MZandtheRaspberryPi/holiday_project_2022/hardware/minibat bot.png

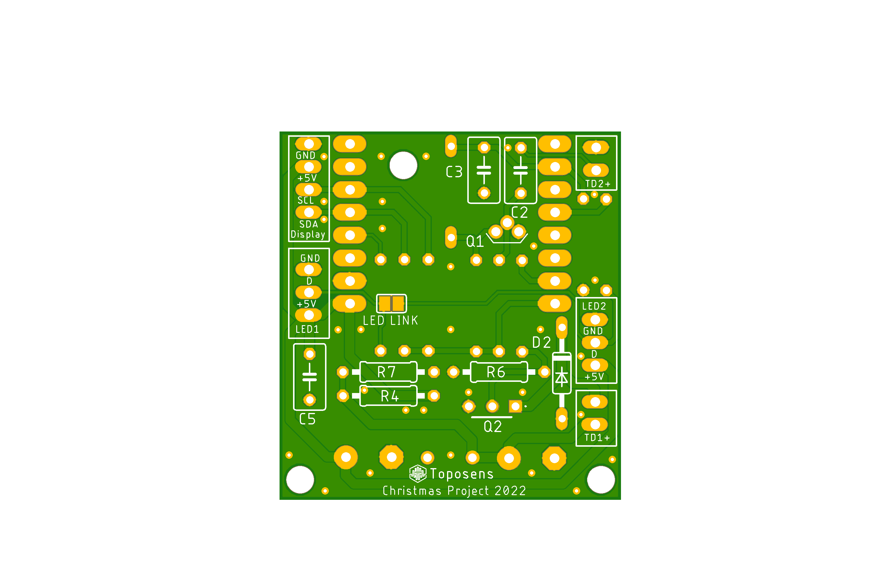
hardware/minibat bot.png
