MZandtheRaspberryPi/holiday_project_2022/firmware/src/oled.cpp

#include "oled.h"

#include <Arduino.h>
#include <Wire.h>
#include <Adafruit_GFX.h>
#include <Adafruit_SSD1306.h>

#include "pins.h"
#include "animate_face.h"

#define SCREEN_BUFFER_HEIGHT    (SCREEN_HEIGHT / 8) // 8 Pixel in a column are packed into one byte

Adafruit_SSD1306 display(SCREEN_WIDTH, SCREEN_HEIGHT, &Wire, -1, 400000, 400000);
static bool showAdcData = false;

void Show_ADC_Data(bool show)
{
    showAdcData = show;
}

void Frame_Shift(FRAME_ShiftDirection_e direction, FRAME_Part_e framePart = FRAME_PART_FULL)
{
    uint8_t height = framePart == FRAME_PART_FULL ? SCREEN_BUFFER_HEIGHT : SCREEN_BUFFER_HEIGHT / 2;
    uint16_t offset = framePart == FRAME_PART_BOT ? (SCREEN_WIDTH * SCREEN_BUFFER_HEIGHT / 2) : 0;
    uint8_t* displayBuffer = display.getBuffer();

    if (direction == FRAME_SHIFT_RIGHT)
    {
        for (int h = 0; h < height; ++h)
        {
            for (int w = (SCREEN_WIDTH - 1); w >= 0; --w)
            {
                uint16_t index = offset + (h * SCREEN_WIDTH) + w;

                if (w == 0)
                    displayBuffer[index] = 0;
                else
                    displayBuffer[index] = displayBuffer[index - 1];
            }
        }
    }
    else
    {
        for (int h = 0; h < height; ++h)
        {
            for (int w = 0; w < SCREEN_WIDTH; ++w)
            {
                uint16_t index = offset + (h * SCREEN_WIDTH) + w;

                if (w == (SCREEN_WIDTH - 1))
                    displayBuffer[index] = 0;
                else
                    displayBuffer[index] = displayBuffer[index + 1];
            }
        }
    }
}

void Frame_Clear(FRAME_Part_e framePart = FRAME_PART_FULL)
{
    uint16_t size = framePart == FRAME_PART_FULL ? SCREEN_WIDTH * SCREEN_BUFFER_HEIGHT : SCREEN_WIDTH * SCREEN_BUFFER_HEIGHT / 2;
    uint16_t offset = framePart == FRAME_PART_BOT ? SCREEN_WIDTH * SCREEN_BUFFER_HEIGHT / 2 : 0;
    uint8_t* displayBuffer = display.getBuffer();

    memset(&displayBuffer[0 + offset], 0, size);
}

void Timeline_Draw_Data_Point(uint16_t dataPoint, uint16_t scale, FRAME_Part_e framePart)
{
    if (!showAdcData)
        return;

    uint8_t height = framePart == FRAME_PART_FULL ? SCREEN_HEIGHT : SCREEN_HEIGHT / 2;
    uint8_t offset = framePart == FRAME_PART_BOT ? (SCREEN_HEIGHT / 2) : 0;
    float scaleFactor = (float)height / scale;
    int16_t pointY = scaleFactor * dataPoint;

    if (pointY > (height - 1))
        pointY = height - 1;
    else if (pointY < 0)
        pointY = 0;

    Frame_Shift(FRAME_SHIFT_LEFT, framePart);

    display.drawPixel(SCREEN_WIDTH - 1, (offset + height - 1) - pointY, SSD1306_WHITE);
    // display.drawPixel(SCREEN_WIDTH - 1, (offset + height - 1), SSD1306_WHITE); // draw zero line

    display.display();
}

void Plot_ADC_Dump(uint16_t* data, uint16_t size)
{
    if (!showAdcData)
        return;

    uint8_t lines = size > SCREEN_WIDTH ? 2 : 1;
    uint16_t plotHeight = SCREEN_HEIGHT / lines;
    uint16_t maxDataVal = plotHeight - 1;

    if (size > (SCREEN_WIDTH * 2))
        size = SCREEN_WIDTH * 2;

    Frame_Clear();

    for (int line = 0; line < lines; ++line)
    {
        uint8_t lineLength;
        if (size < SCREEN_WIDTH)
        {
            lineLength = size;
        }
        else
        {
            lineLength = SCREEN_WIDTH;
        }
        size -= lineLength;

        for (int i = 0; i < lineLength; ++i)
        {
            uint16_t dataPoint = data[i + (line * SCREEN_WIDTH)] / 16;

            if (dataPoint > maxDataVal)
                dataPoint = maxDataVal;

            display.drawPixel(i, (maxDataVal + (plotHeight * line)) - dataPoint, SSD1306_WHITE);
            display.drawPixel(i, (maxDataVal + (plotHeight * line)), SSD1306_WHITE);
        }
    }

    display.display();
}

void Display_Default_HomeScreen(void)
{
    display.setTextSize(1);
    display.setTextColor(WHITE);
    display.setCursor(30, 12);
    display.println("Good Morning!");
    display.display();
    // delay(2);

    // display.clearDisplay();
}


bool Task_OLED_Setup(void)
{
#ifdef CUSTOM_I2C_PINS
    Wire.begin(PIN_WIRE_SDA_CUSTOM, PIN_WIRE_SCL_CUSTOM);
#endif
    if(!display.begin(SSD1306_SWITCHCAPVCC, 0x3C)) {
        Serial.println(F("SSD1306 allocation failed"));
        for(;;);
    }
    Wire.setClock(400000);
    // Display_Default_HomeScreen();
    displayFace(0, 0, 0);
    return true;
}

void Task_OLED_Periodic(void)
{
    // if we are in adc dump mode, show graph
    // else show face
    if (!showAdcData)
        animateFace();
}
