MZandtheRaspberryPi/holiday_project_2022/firmware/src/oled.h

#ifndef OLED_H
#define OLED_H

#include "stdint.h"

#define TASK_OLED_FREQUENCY 30                             // Hz
#define TASK_OLED_INTERVAL  (1000 / TASK_OLED_FREQUENCY)   // ms

#define SCREEN_WIDTH        128 // OLED display width, in pixels
#define SCREEN_HEIGHT       64 // OLED display height, in pixels

typedef enum {
    FRAME_SHIFT_LEFT = 0,
    FRAME_SHIFT_RIGHT
}FRAME_ShiftDirection_e;

typedef enum {
    FRAME_PART_FULL = 0,
    FRAME_PART_TOP,
    FRAME_PART_BOT
}FRAME_Part_e;

bool Task_OLED_Setup(void);
void Task_OLED_Periodic(void);
void Timeline_Draw_Data_Point(uint16_t dataPoint, uint16_t scale, FRAME_Part_e framePart = FRAME_PART_FULL);
void Plot_ADC_Dump(uint16_t* data, uint16_t size);
void Show_ADC_Data(bool show);

#endif // OLED_H
