MZandtheRaspberryPi/holiday_project_2022/firmware/src/led.h

#ifndef LED_H
#define LED_H

#include "stdint.h"

#define TASK_LED_FREQUENCY  100                         // Hz
#define TASK_LED_INTERVAL   (1000 / TASK_LED_FREQUENCY) // ms

#define LEDS_PER_STRING     5
#define BRIGHTNESS          100

typedef struct Color_t
{
    uint8_t red;
    uint8_t green;
    uint8_t blue;
}Color_t;

void LED_Switch_Mode(void);
void LED_Trigger_Action_Mode(void);
bool Task_LED_Setup(void);
void Task_LED_Periodic(void);

#endif // LED_H
